Slartitorto/BARS1/HARDWARE/sensor/1.65/BARS1_1.65 PCB pdf/BARS1_1.65_etch_paste_mask_bottom_mirror.pdf

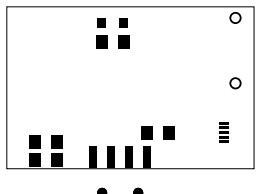
[picture p3: figure]
