Slartitorto/BARS1/HARDWARE/sensor/1.66/BARS1_1.66 PCB pdf/BARS1_1.66_etch_silk_top_mirror.pdf

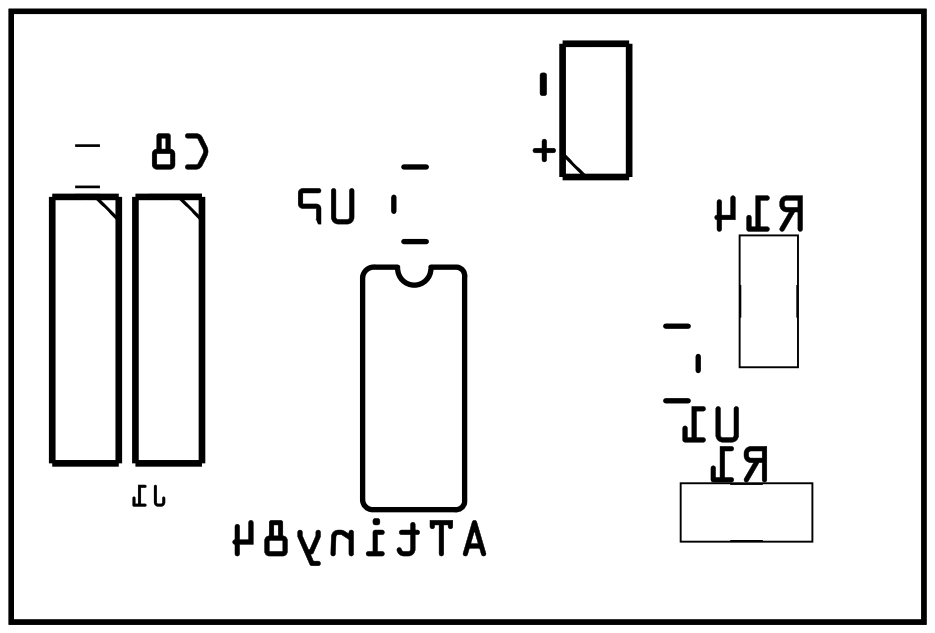
[picture p20: page 1]
