Slartitorto/BARS1/HARDWARE/receiver/1.1/BARS1_esp8266_1.1_pdf/BARS1_esp8266_1.1_etch_mask_bottom.pdf

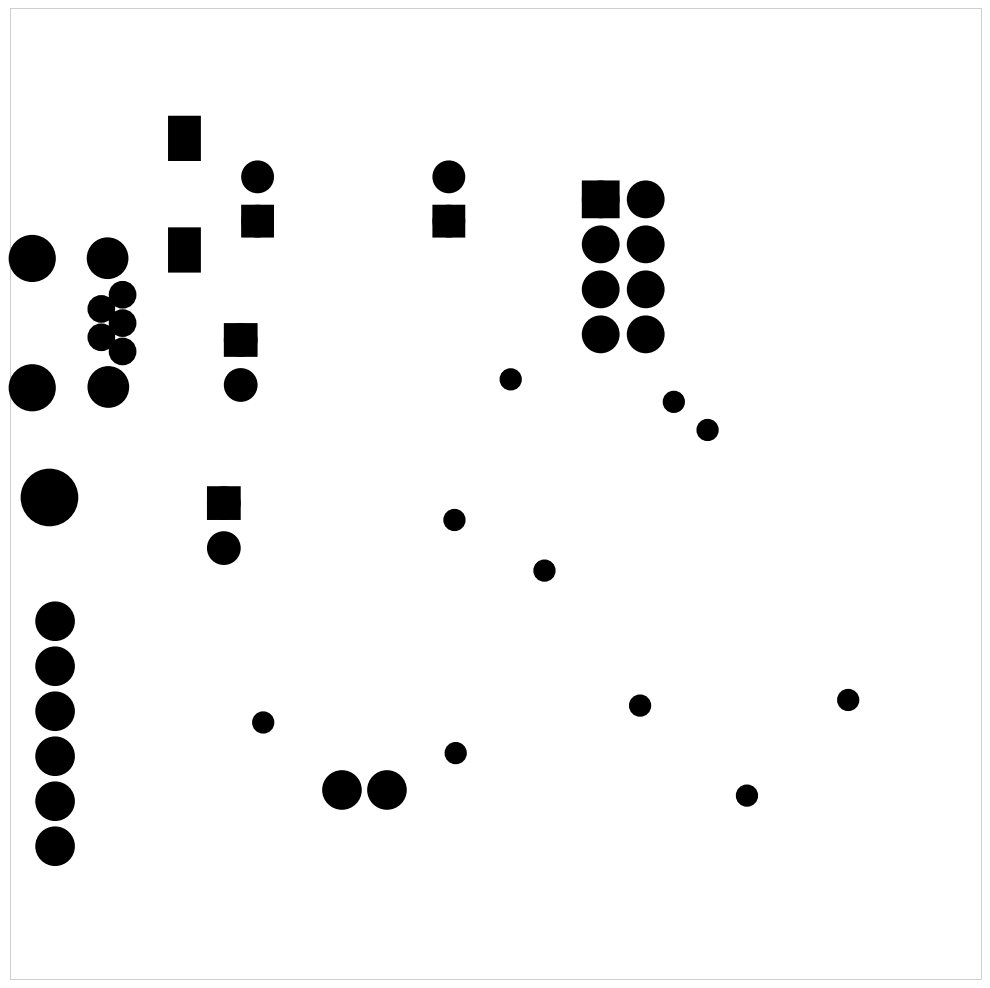
[picture p25: page 1]
