Slartitorto/BARS1/HARDWARE/receiver/1.1/BARS1_esp8266_1.1_pdf/BARS1_esp8266_1.1_etch_mask_bottom_mirror.pdf

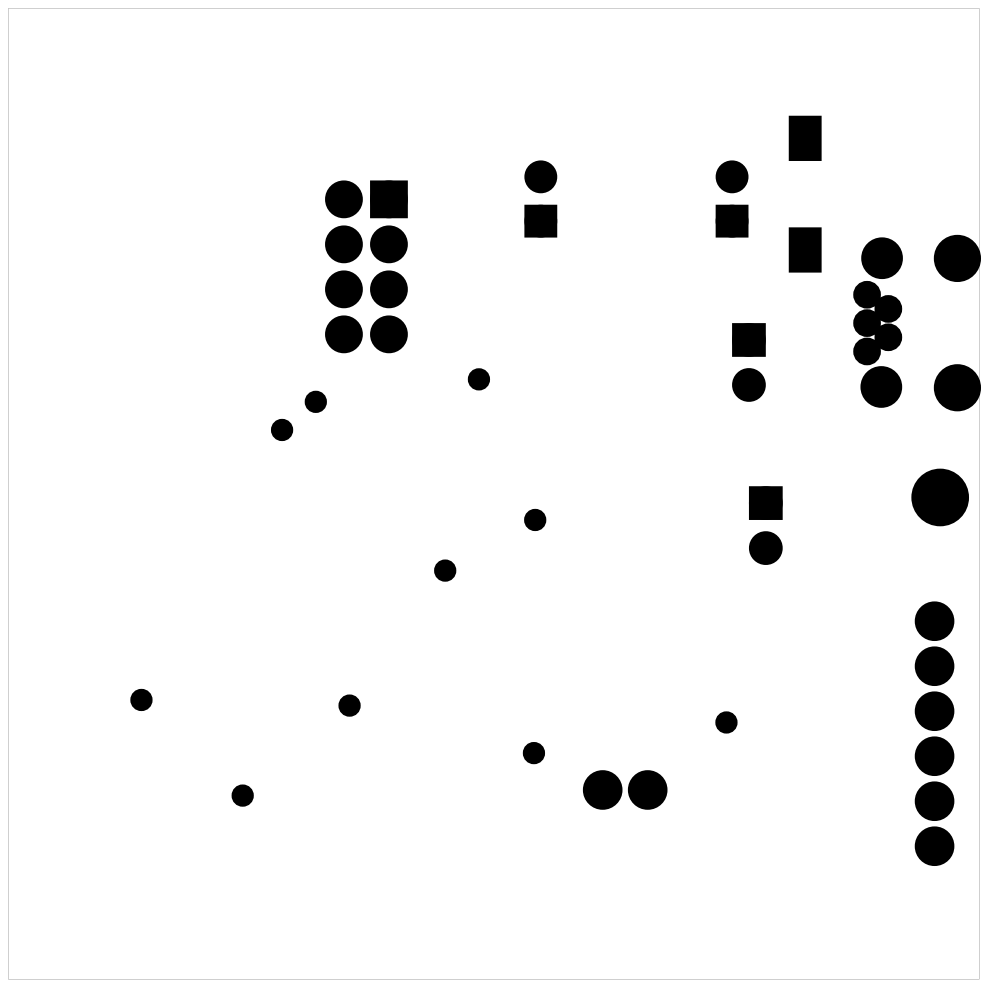
[picture p26: page 1]
