Slartitorto/BARS1/HARDWARE/receiver/1.0/BARS1_esp8266_1.0 PCB pdf/BARS1_esp8266_etch_copper_top.pdf

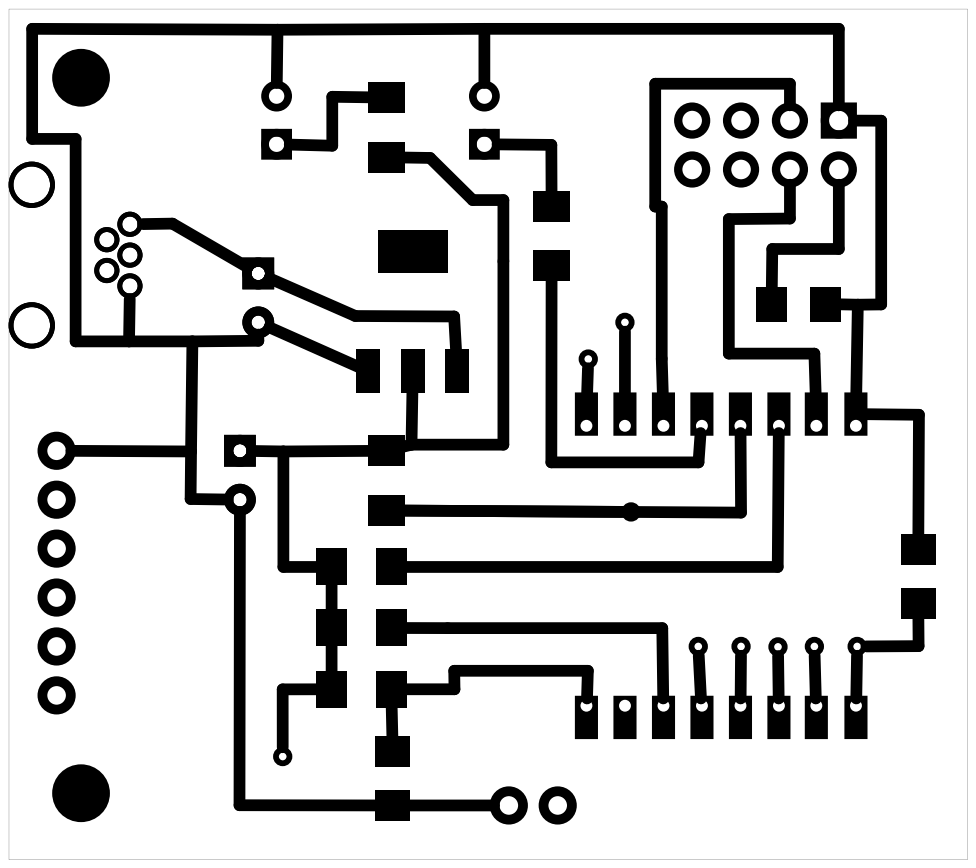
[picture p37: page 1]
