Slartitorto/BARS1/HARDWARE/receiver/1.0/BARS1_esp8266_1.0 PCB pdf/BARS1_esp8266_etch_paste_mask_top_mirror.pdf

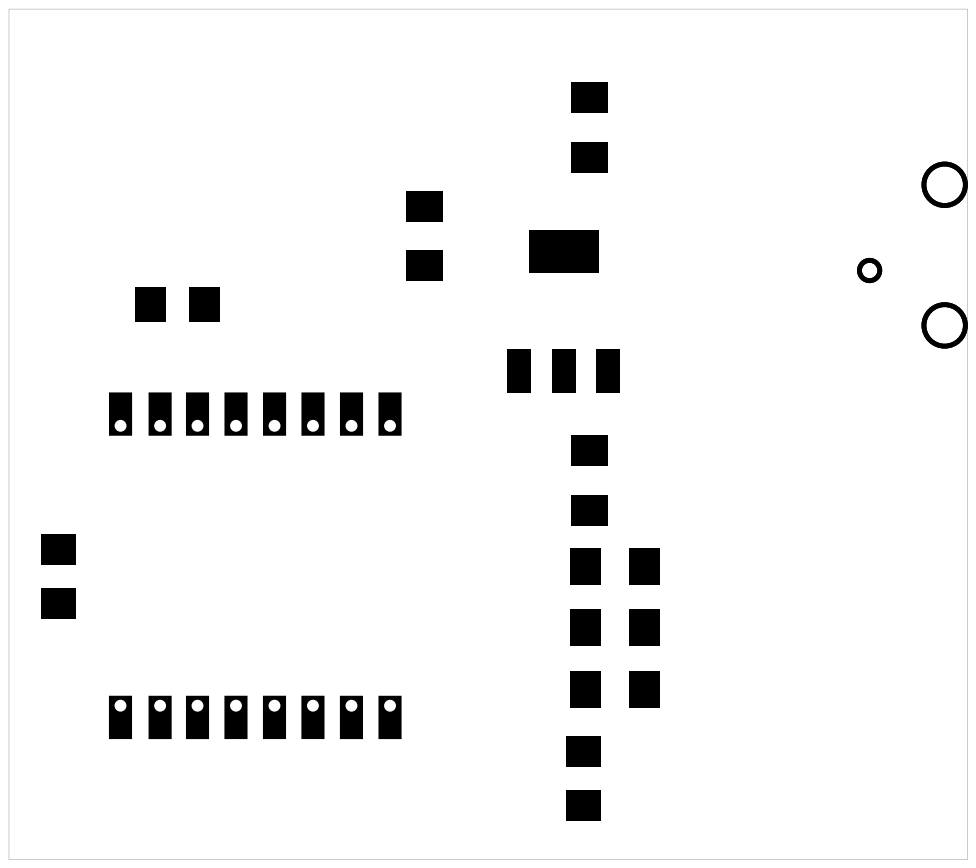
[picture p44: page 1]
