Slartitorto/BARS1/HARDWARE/sensor/1.65/BARS1_1.65 PCB pdf/BARS1_1.65_etch_copper_bottom_mirror.pdf

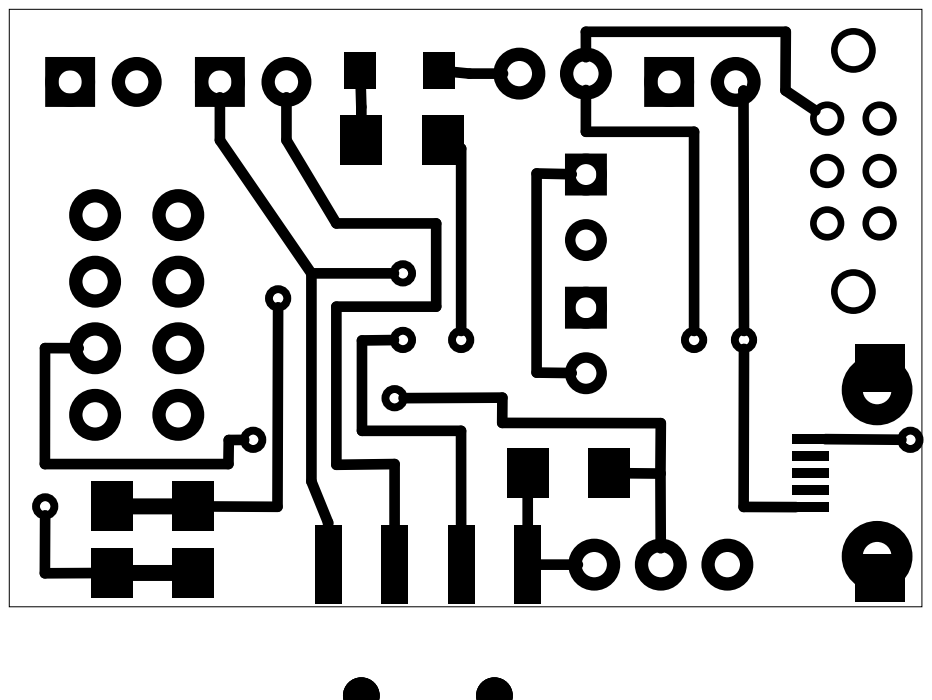
[picture p50: page 1]
