Slartitorto/BARS1/HARDWARE/sensor/1.65/BARS1_1.65 PCB pdf/BARS1_1.65_etch_mask_bottom_mirror.pdf

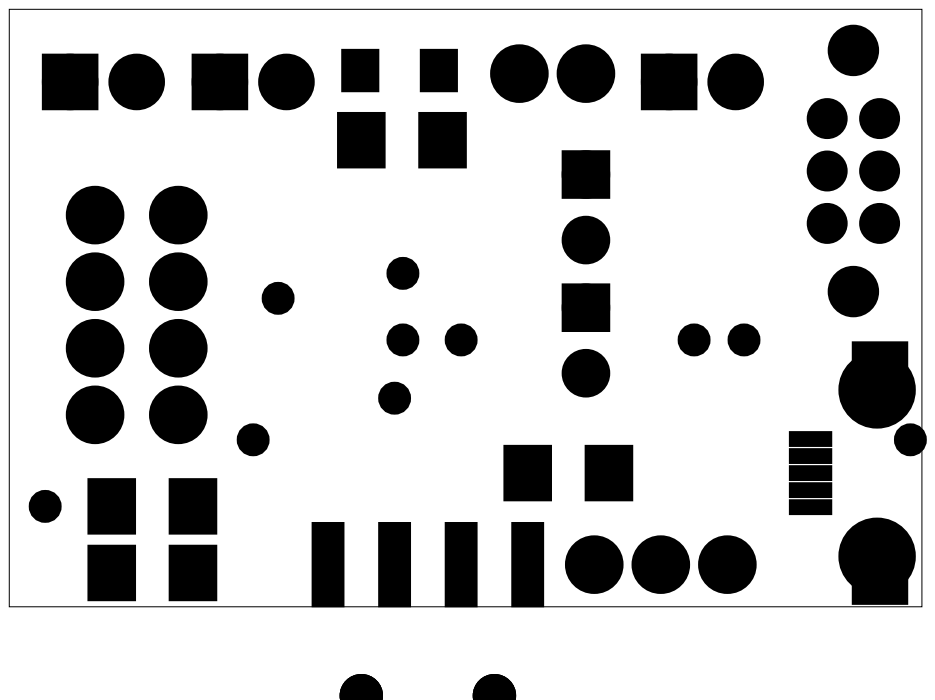
[picture p54: page 1]
