Slartitorto/BARS1/HARDWARE/sensor/1.65/BARS1_1.65 PCB pdf/BARS1_1.65_etch_mask_top_mirror.pdf

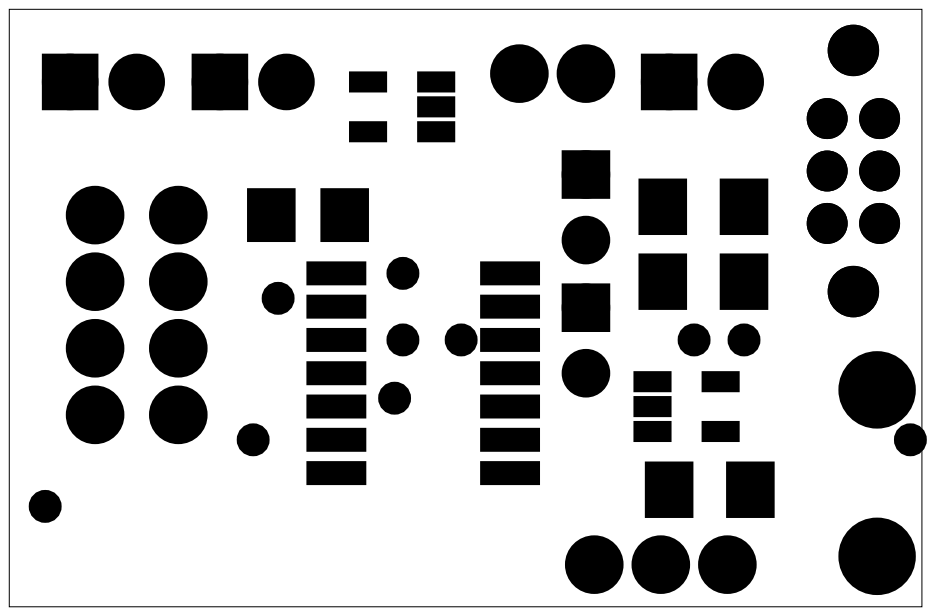
[picture p56: page 1]
