Slartitorto/BARS1/HARDWARE/sensor/1.65/BARS1_1.65 PCB pdf/BARS1_1.65_etch_silk_bottom_mirror.pdf

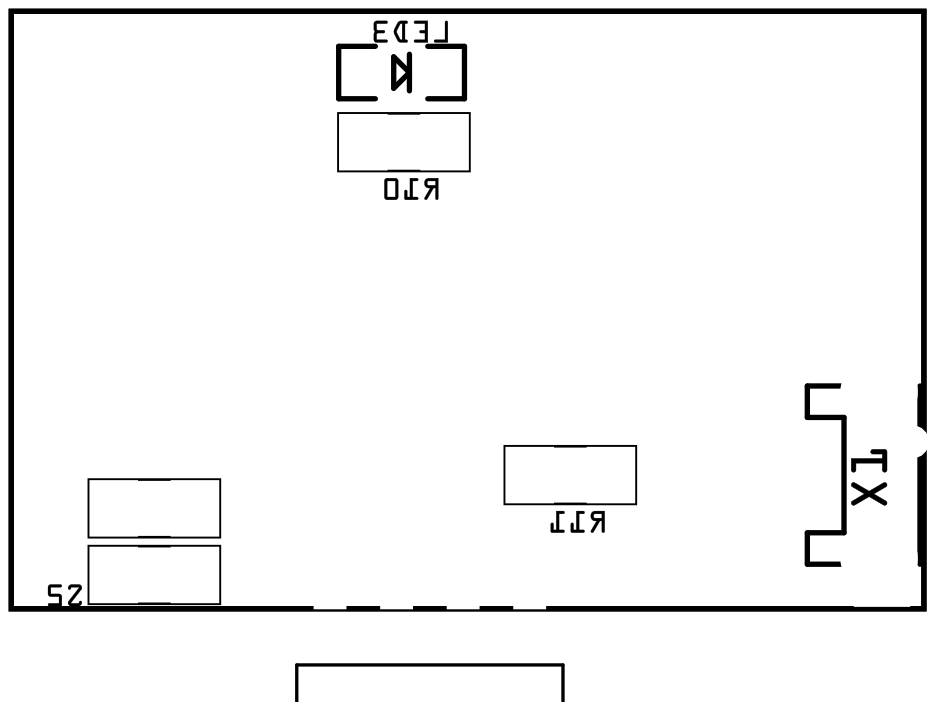
[picture p58: page 1]
